itzandroidtab/totp/ui/splash.hpp

#pragma once

#include <klib/graphics/bitmap.hpp>

#include <storage.hpp>

#include "screen.hpp"

namespace menu {
    template <typename FrameBuffer, typename Storage, typename Rtc, typename Usb>
    class splash: public screen<FrameBuffer> {
    protected:
        using color = klib::graphics::color;
        using screen_base = screen<FrameBuffer>;

        // bootup splash screen
        constexpr static auto bitmap = klib::graphics::bitmap<50, 66, klib::graphics::mode::rgb242>(
            color{0x00, 0x00, 0x00}, color{0x00, 0x00, 0x00}, color{0x00, 0x00, 0x00}, color{0x00, 0x00, 0x00}, color{0x00, 0x00, 0x00}, color{0x00, 0x00, 0x00}, color{0x00, 0x00, 0x00}, color{0x00, 0x00, 0x00}, color{0x00, 0x00, 0x00}, color{0x00, 0x00, 0x00}, color{0x00, 0x00, 0x00}, color{0x00, 0x00, 0x00}, color{0x00, 0x00, 0x00}, color{0x00, 0x00, 0x00}, color{0x00, 0x00, 0x00}, color{0x00, 0x00, 0x00}, color{0x00, 0x00, 0x00}, color{0x00, 0x00, 0x00}, color{0x00, 0x00, 0x00}, color{0x00, 0x00, 0x00}, color{0x00, 0x00, 0x00}, color{0x00, 0x00, 0x00}, color{0x00, 0x00, 0x00}, color{0x00, 0x00, 0x00}, color{0x00, 0x00, 0x00}, color{0xff, 0xff, 0xff}, color{0x00, 0x00, 0x00}, color{0x00, 0x00, 0x00}, color{0x00, 0x00, 0x00}, color{0x00, 0x00, 0x00}, color{0x00, 0x00, 0x00}, color{0x00, 0x00, 0x00}, color{0x00, 0x00, 0x00}, color{0x00, 0x00, 0x00}, color{0x00, 0x00, 0x00}, color{0x00, 0x00, 0x00}, color{0x00, 0x00, 0x00}, color{0x00, 0x00, 0x00}, color{0x00, 0x00, 0x00}, color{0x00, 0x00, 0x00}, color{0x00, 0x00, 0x00}, color{0x00, 0x00, 0x00}, color{0x00, 0x00, 0x00}, color{0x00, 0x00, 0x00}, color{0x00, 0x00, 0x00}, color{0x00, 0x00, 0x00}, color{0x00, 0x00, 0x00}, color{0x00, 0x00, 0x00}, color{0x00, 0x00, 0x00}, color{0x00, 0x00, 0x00}, 
            color{0x00, 0x00, 0x00}, color{0x00, 0x00, 0x00}, color{0x00, 0x00, 0x00}, color{0x00, 0x00, 0x00}, color{0x00, 0x00, 0x00}, color{0x00, 0x00, 0x00}, color{0x00, 0x00, 0x00}, color{0x00, 0x00, 0x00}, color{0x00, 0x00, 0x00}, color{0x00, 0x00, 0x00}, color{0x00, 0x00, 0x00}, color{0x00, 0x00, 0x00}, color{0x00, 0x00, 0x00}, color{0x00, 0x00, 0x00}, color{0x00, 0x00, 0x00}, color{0x00, 0x00, 0x00}, color{0x00, 0x00, 0x00}, color{0x00, 0x00, 0x00}, color{0x00, 0x00, 0x00}, color{0xff, 0xff, 0xff}, color{0x00, 0x00, 0x00}, color{0xff, 0xff, 0xff}, color{0xff, 0xff, 0xff}, color{0xff, 0xff, 0xff}, color{0xff, 0xff, 0xff}, color{0xff, 0xff, 0xff}, color{0xff, 0xff, 0xff}, color{0xff, 0xff, 0xff}, color{0xff, 0xff, 0xff}, color{0x00, 0x00, 0x00}, color{0xff, 0xff, 0xff}, color{0x00, 0x00, 0x00}, color{0x00, 0x00, 0x00}, color{0x00, 0x00, 0x00}, color{0x00, 0x00, 0x00}, color{0x00, 0x00, 0x00}, color{0x00, 0x00, 0x00}, color{0x00, 0x00, 0x00}, color{0x00, 0x00, 0x00}, color{0x00, 0x00, 0x00}, color{0x00, 0x00, 0x00}, color{0x00, 0x00, 0x00}, color{0x00, 0x00, 0x00}, color{0x00, 0x00, 0x00}, color{0x00, 0x00, 0x00}, color{0x00, 0x00, 0x00}, color{0x00, 0x00, 0x00}, color{0x00, 0x00, 0x00}, color{0x00, 0x00, 0x00}, color{0x00, 0x00, 0x00}, 
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
            color{0x00, 0x00, 0x00}, color{0x00, 0x00, 0x00}, color{0xff, 0xff, 0xff}, color{0xff, 0xff, 0xff}, color{0xff, 0xff, 0xff}, color{0xff, 0xff, 0xff}, color{0xff, 0xff, 0xff}, color{0xff, 0xff, 0xff}, color{0xff, 0xff, 0xff}, color{0xff, 0xff, 0xff}, color{0xff, 0xff, 0xff}, color{0xff, 0xff, 0xff}, color{0xff, 0xff, 0xff}, color{0xff, 0xff, 0xff}, color{0xff, 0xff, 0xff}, color{0xff, 0xff, 0xff}, color{0xff, 0xff, 0xff}, color{0xff, 0xff, 0xff}, color{0xff, 0xff, 0xff}, color{0xff, 0xff, 0xff}, color{0xff, 0xff, 0xff}, color{0xff, 0xff, 0xff}, color{0xff, 0xff, 0xff}, color{0xff, 0xff, 0xff}, color{0xff, 0xff, 0xff}, color{0xff, 0xff, 0xff}, color{0xff, 0xff, 0xff}, color{0xff, 0xff, 0xff}, color{0xff, 0xff, 0xff}, color{0xff, 0xff, 0xff}, color{0xff, 0xff, 0xff}, color{0xff, 0xff, 0xff}, color{0xff, 0xff, 0xff}, color{0xff, 0xff, 0xff}, color{0xff, 0xff, 0xff}, color{0xff, 0xff, 0xff}, color{0xff, 0xff, 0xff}, color{0xff, 0xff, 0xff}, color{0xff, 0xff, 0xff}, color{0xff, 0xff, 0xff}, color{0xff, 0xff, 0xff}, color{0xff, 0xff, 0xff}, color{0xff, 0xff, 0xff}, color{0xff, 0xff, 0xff}, color{0xff, 0xff, 0xff}, color{0xff, 0xff, 0xff}, color{0xff, 0xff, 0xff}, color{0xff, 0xff, 0xff}, color{0x00, 0x00, 0x00}, color{0x00, 0x00, 0x00}
        );

    public:
        splash() {}

        virtual void deactivate(const screen_id id) override {
            // init all the hardware we did not initialize yet
            // init the rtc
            Rtc::init();

            // init the storage for all the keys
            Storage::init({}, 
                reinterpret_cast<uint32_t>(&__profiles_start), 
                reinterpret_cast<uint32_t>(&__profiles_end)
            );

            // init the usb driver + device
            Usb::init();
        };

        virtual void main(const klib::time::us delta, const input::buttons& buttons) override {
            // switch to the main app to trigger a deactivate and 
            // we can init all the hardware
            screen_base::buffer.change(screen_id::totp, false);
        }

        virtual void draw(FrameBuffer& frame_buffer, const klib::vector2u& offset) override {
            // clear the background black
            frame_buffer.clear(klib::graphics::black);

            // override with the bitmap we want to draw
            bitmap.draw(
                frame_buffer, 
                klib::vector2i{95, 34} - offset.cast<int32_t>()
            );

            // url to show
            constexpr static char url[] = "koon.io";

            // draw using the small font
            screen_base::small_text::template draw<FrameBuffer>(
                frame_buffer, url, 
                klib::vector2i{
                    240 - (
                        klib::string::strlen(url) * screen_base::small_text::font::width
                    ), 120
                } - offset.cast<int32_t>(), 
                klib::graphics::white
            );
        }
    };
}
